nicohmje/WaveMaker/WaveMaker_CAD/WM_WaveMaker_base.SLDPRT

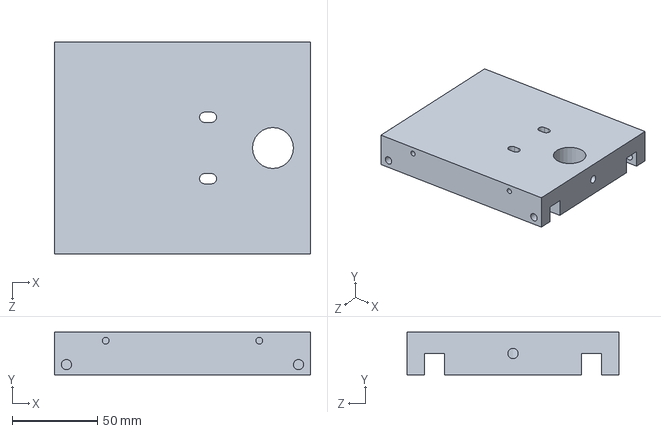
[picture p16: CAD file, 2023-04-07]
WaveMaker_CAD/WM_WaveMaker_base.SLDPRT
150.0 x 25.0 x 124.0 mm
