nicohmje/WaveMaker/WaveMaker_CAD/WM_WaveMaker_USB-B_Mount.SLDPRT

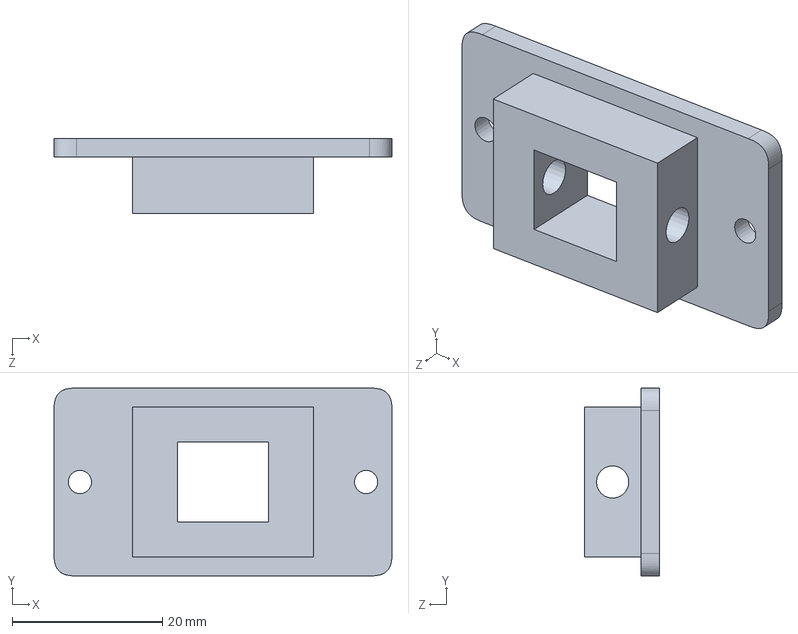
[picture p17: CAD file, 2023-04-07]
WaveMaker_CAD/WM_WaveMaker_USB-B_Mount.SLDPRT
45.0 x 25.0 x 10.0 mm
